andreistan26/ebook-reader/Images/image1.png

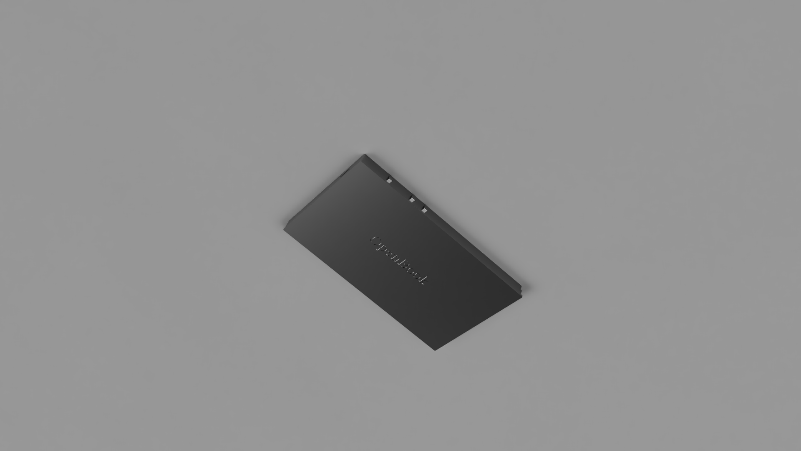
Images/image1.png
