andreistan26/ebook-reader/Images/image2.png

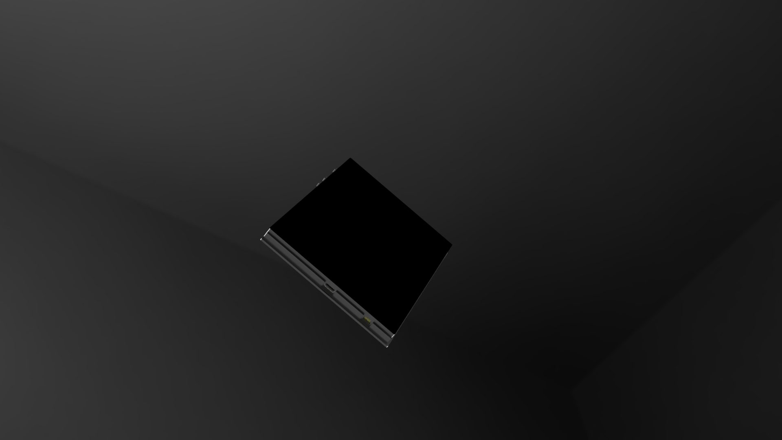
Images/image2.png
