andreistan26/ebook-reader/Images/image3.png

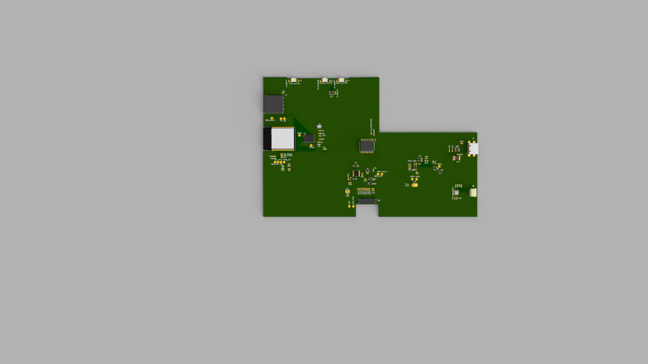
Images/image3.png
